kuehlingkuehling/RepRap-Industrial/DXF/frame-enclosure_base-bottom.dxf

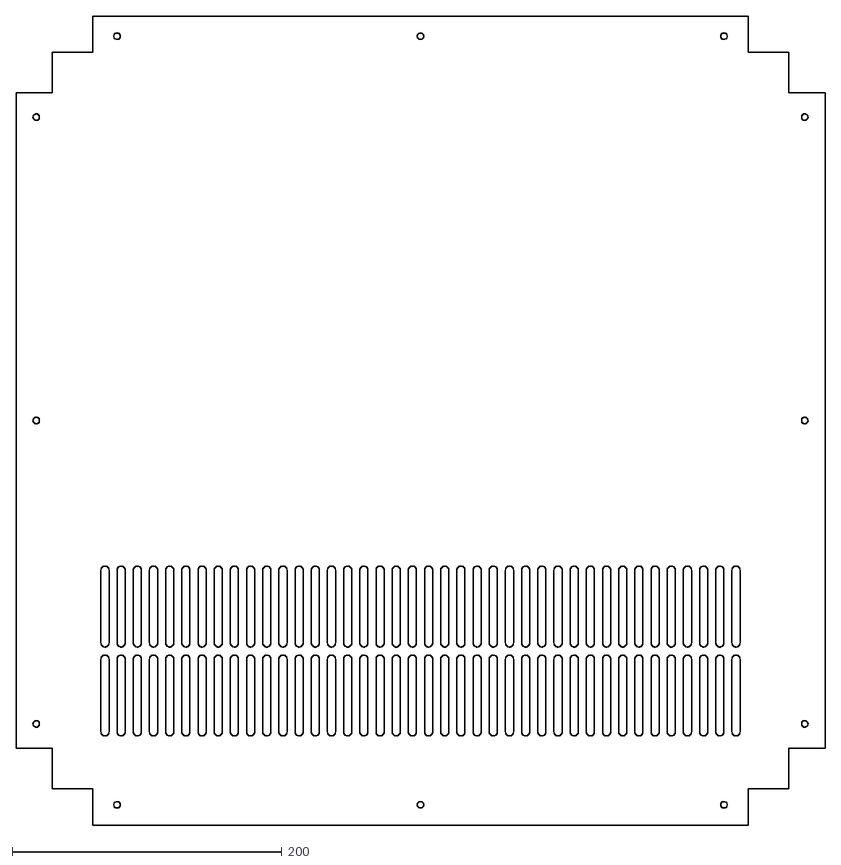
[picture p15: CAD file, 2014-06-27]
DXF/frame-enclosure_base-bottom.dxf
600.0 x 600.0
