kuehlingkuehling/RepRap-Industrial/STL/18___air-filter_activatedcarbon-container-lid.stl

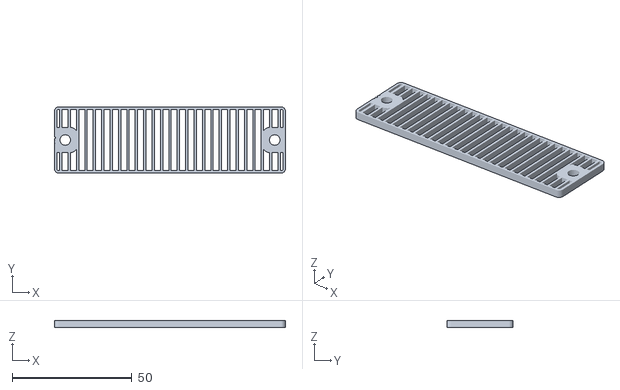
[picture p16: CAD file, 2015-10-23]
STL/18___air-filter_activatedcarbon-container-lid.stl
96.3 x 27.6 x 3.00
