kuehlingkuehling/RepRap-Industrial/DXF/frame-enclosure_chamber-top.dxf

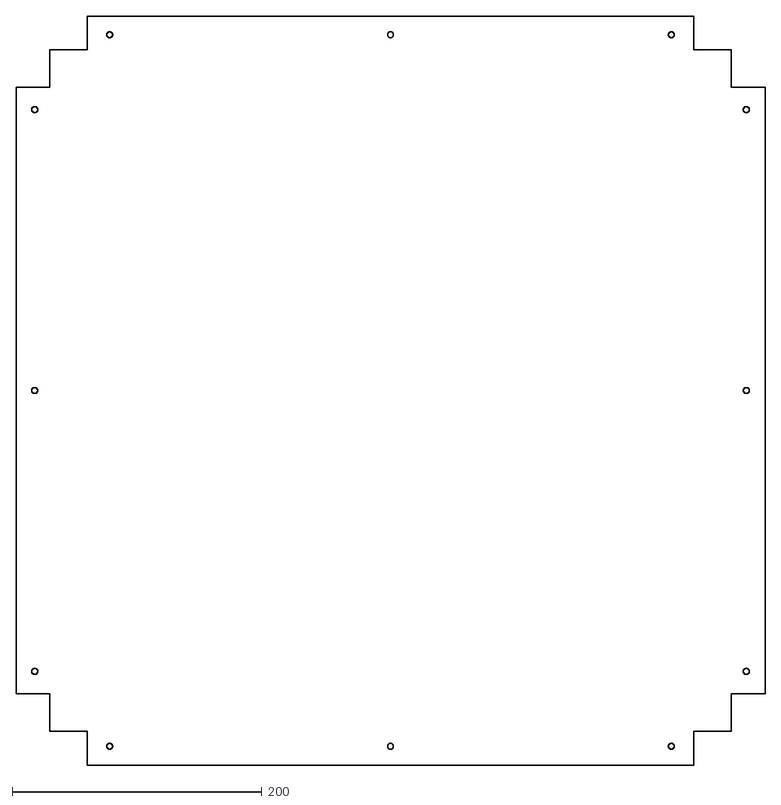
[picture p17: CAD file, 2014-06-27]
DXF/frame-enclosure_chamber-top.dxf
600.0 x 600.0
