kuehlingkuehling/RepRap-Industrial/STL/70___frame-corner_door-top-right.stl

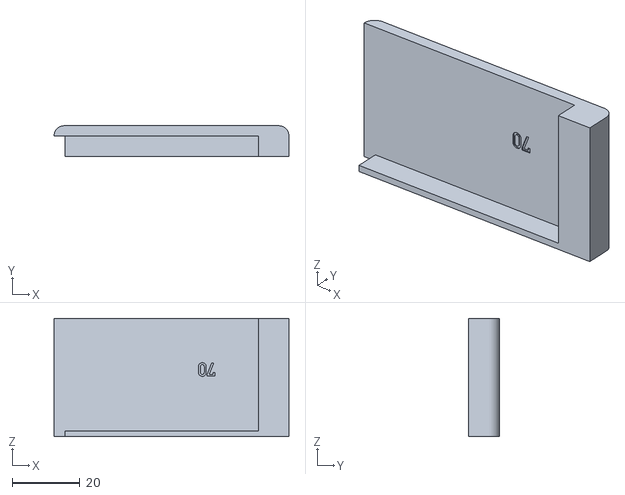
[picture p18: CAD file, 2015-10-23]
STL/70___frame-corner_door-top-right.stl
69.2 x 8.99 x 34.8
