kuehlingkuehling/RepRap-Industrial/DXF/frame-enclosure_base-front.dxf

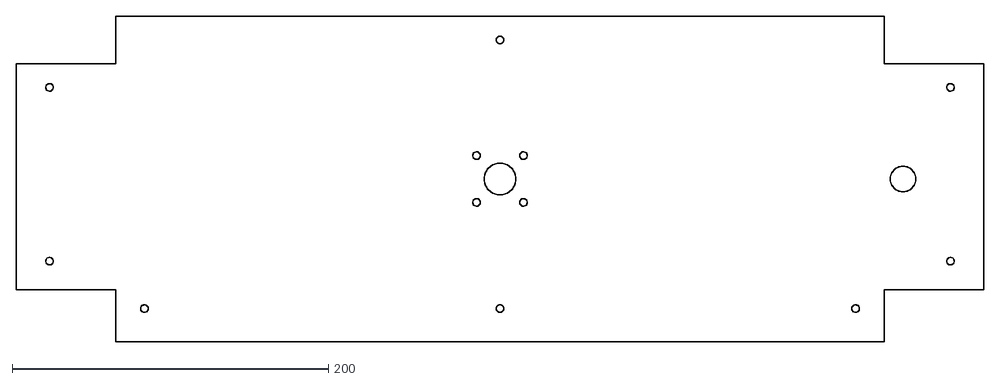
[picture p19: CAD file, 2014-06-27]
DXF/frame-enclosure_base-front.dxf
612.0 x 206.0
