kuehlingkuehling/RepRap-Industrial/STL/23___z-end_top.stl

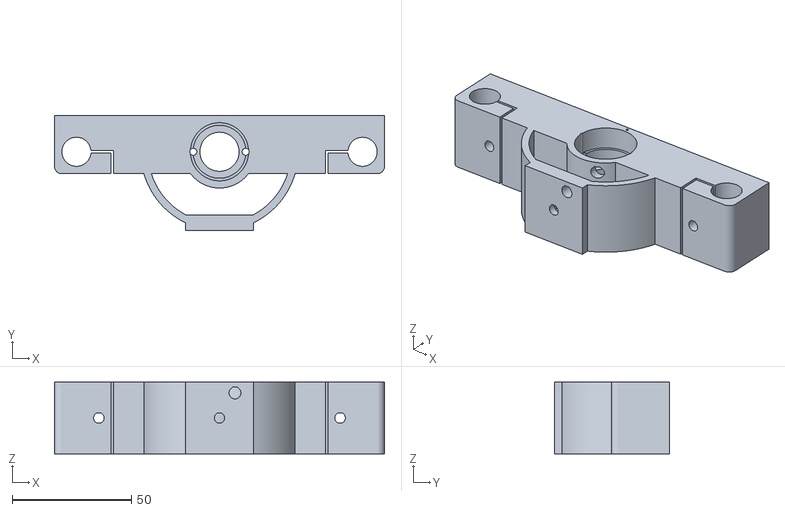
[picture p20: CAD file, 2015-10-23]
STL/23___z-end_top.stl
138.4 x 48.2 x 30.0
