kuehlingkuehling/RepRap-Industrial/STL/290___led-mount_right.stl

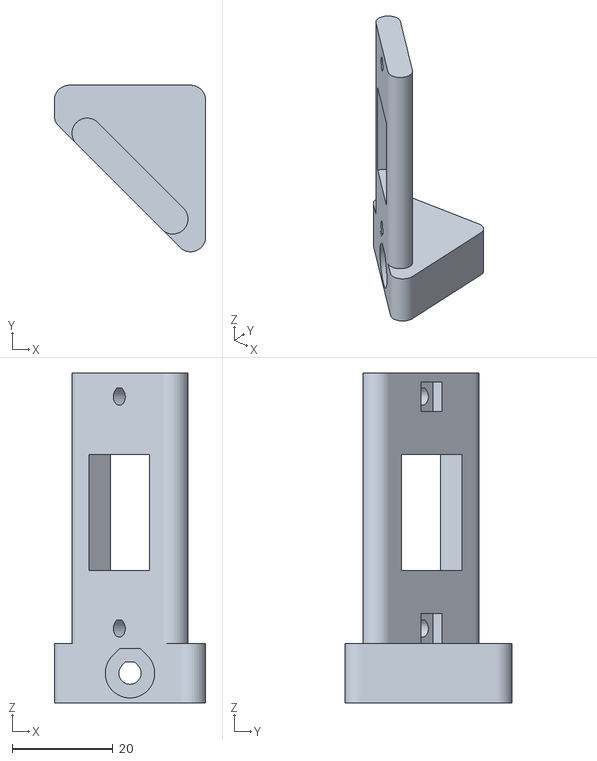
[picture p21: CAD file, 2015-10-23]
STL/290___led-mount_right.stl
30.0 x 33.0 x 65.3
