kuehlingkuehling/RepRap-Industrial/STL/335___bed-corner_front-right_back-left.stl

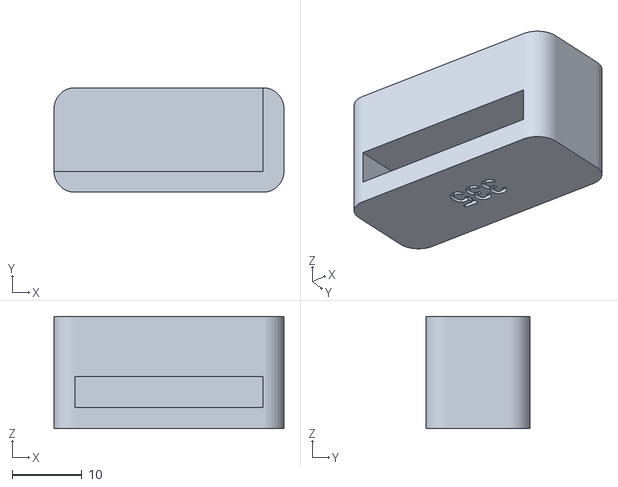
[picture p22: CAD file, 2015-10-23]
STL/335___bed-corner_front-right_back-left.stl
33.0 x 15.0 x 16.1
