kuehlingkuehling/RepRap-Industrial/STL/22___extruder-front.stl

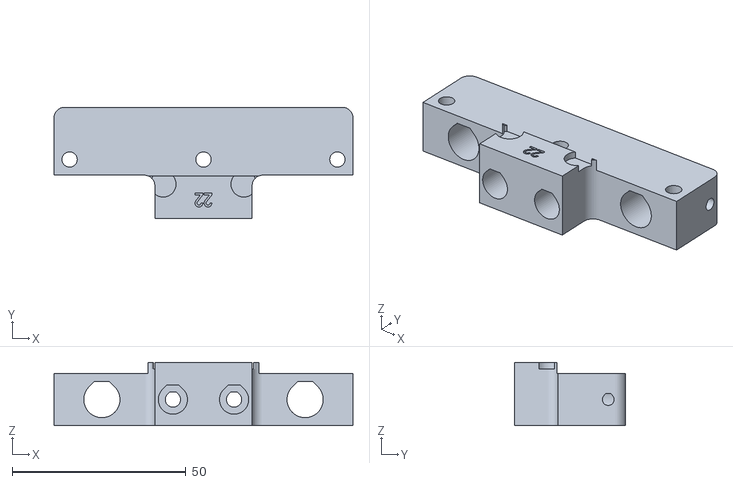
[picture p23: CAD file, 2015-10-23]
STL/22___extruder-front.stl
86.0 x 32.0 x 18.2
