kuehlingkuehling/RepRap-Industrial/STL/264___filament-feed.stl

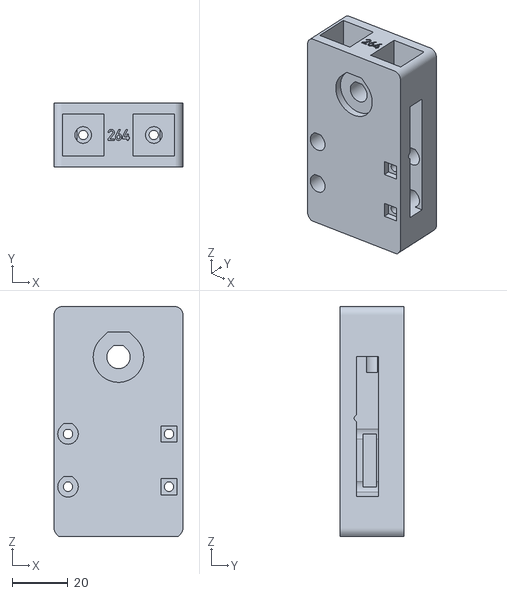
[picture p24: CAD file, 2015-10-23]
STL/264___filament-feed.stl
46.4 x 23.0 x 82.8
