kuehlingkuehling/RepRap-Industrial/STL/29___controller-ethernet-coupling-panel.stl

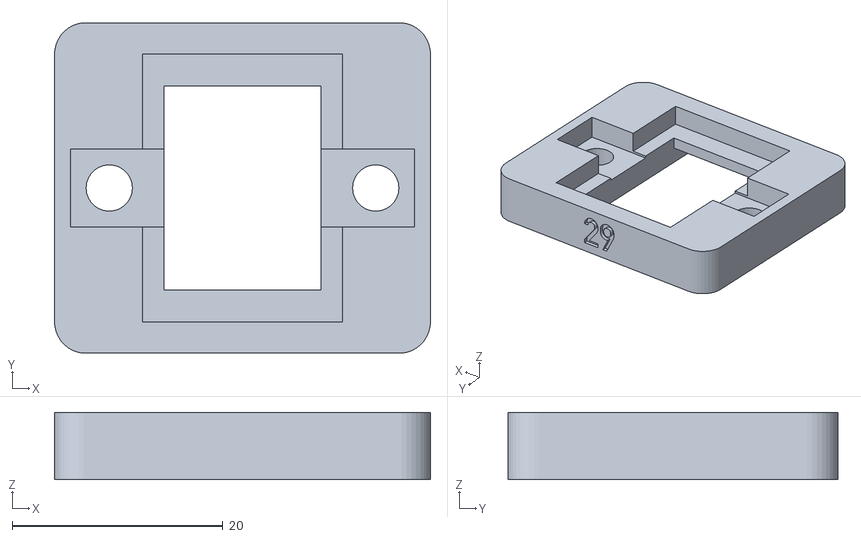
[picture p25: CAD file, 2015-10-23]
STL/29___controller-ethernet-coupling-panel.stl
35.7 x 31.4 x 6.40
