kuehlingkuehling/RepRap-Industrial/STL/53___air-heater-bottom.stl

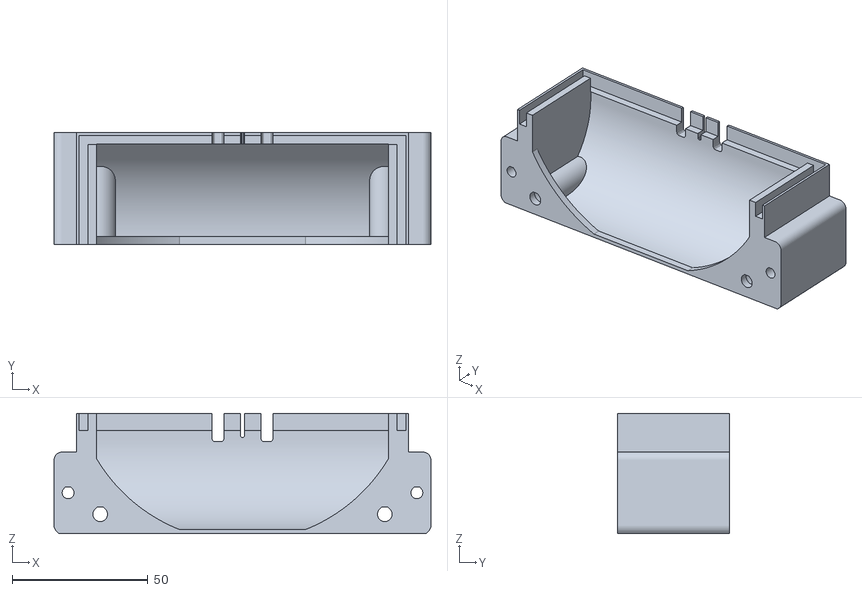
[picture p26: CAD file, 2015-10-23]
STL/53___air-heater-bottom.stl
138.8 x 41.2 x 44.2
