kuehlingkuehling/RepRap-Industrial/STL/31___y-end_back-left.stl

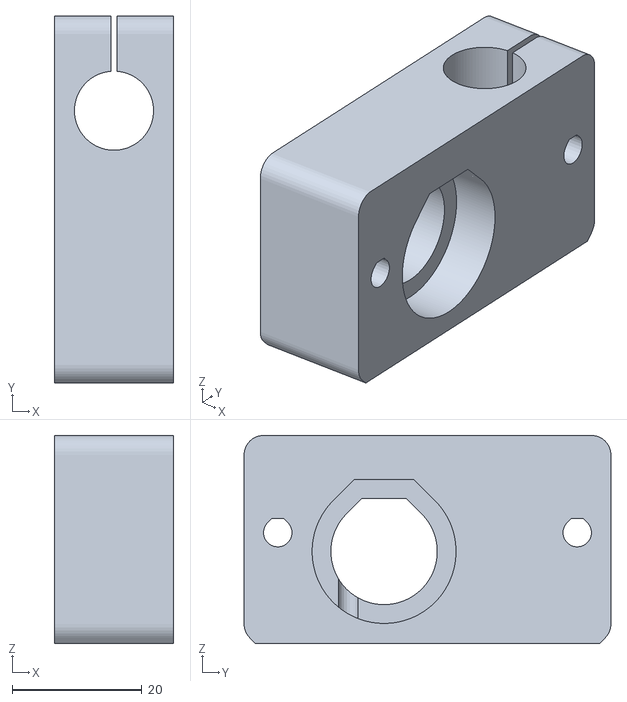
[picture p27: CAD file, 2015-10-23]
STL/31___y-end_back-left.stl
18.4 x 56.6 x 32.1
