kuehlingkuehling/RepRap-Industrial/STL/65___pulley_x-idler_y-idler.stl

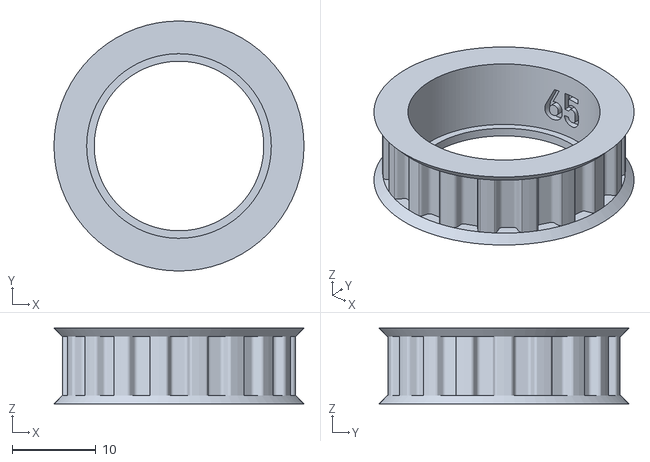
[picture p28: CAD file, 2015-10-23]
STL/65___pulley_x-idler_y-idler.stl
29.8 x 29.8 x 9.00
