kuehlingkuehling/RepRap-Industrial/STL/56___cablechain-mount-y-frame_back.stl

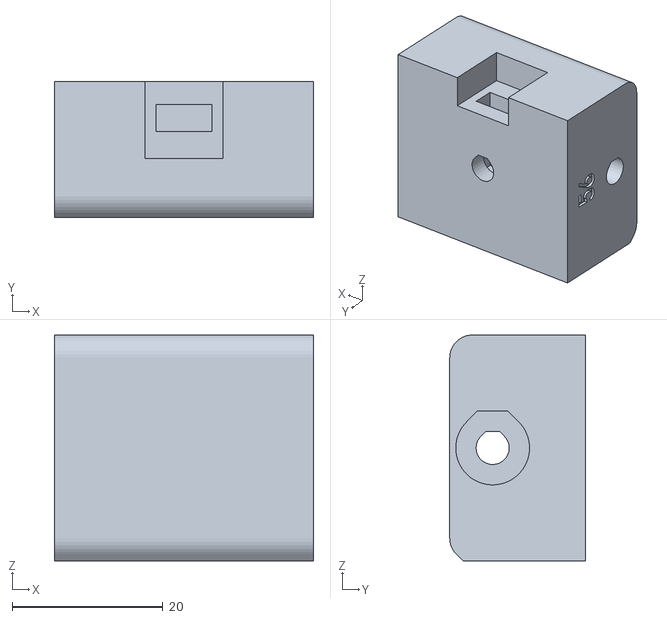
[picture p29: CAD file, 2015-10-23]
STL/56___cablechain-mount-y-frame_back.stl
34.4 x 18.0 x 30.0
