kuehlingkuehling/RepRap-Industrial/STL/17___belt-tensioner_y-right_x.stl

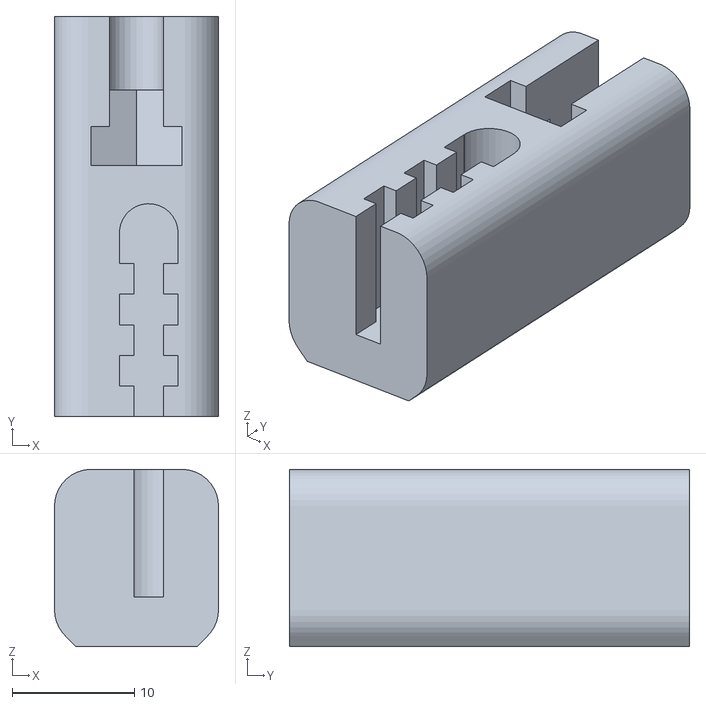
[picture p30: CAD file, 2015-10-23]
STL/17___belt-tensioner_y-right_x.stl
13.4 x 32.7 x 14.5
