kuehlingkuehling/RepRap-Industrial/STL/20___air-filter_activatedcarbon-container.stl

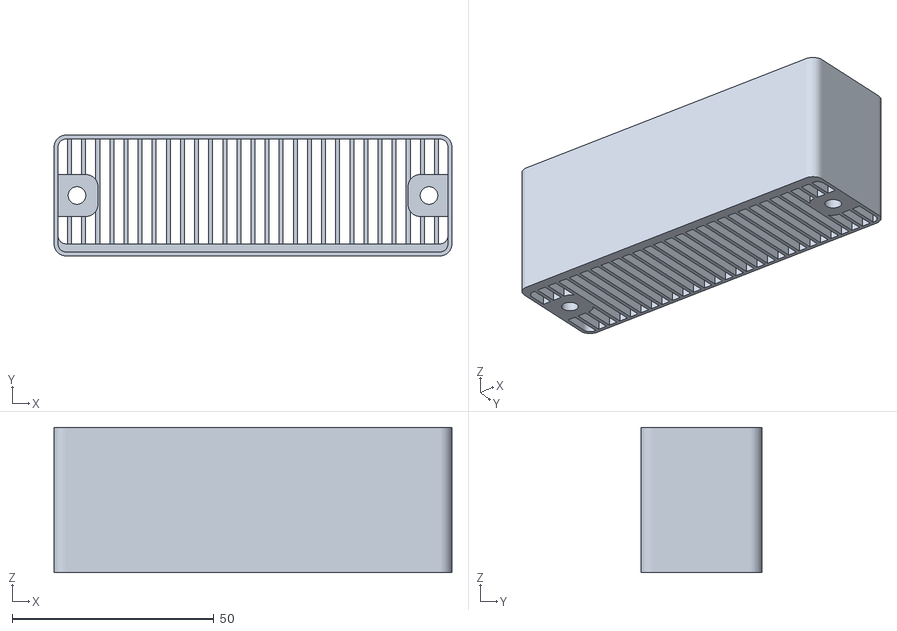
[picture p31: CAD file, 2015-10-23]
STL/20___air-filter_activatedcarbon-container.stl
98.7 x 30.0 x 36.0
