kuehlingkuehling/RepRap-Industrial/STL/13___frame-enclosure-door-handle.stl

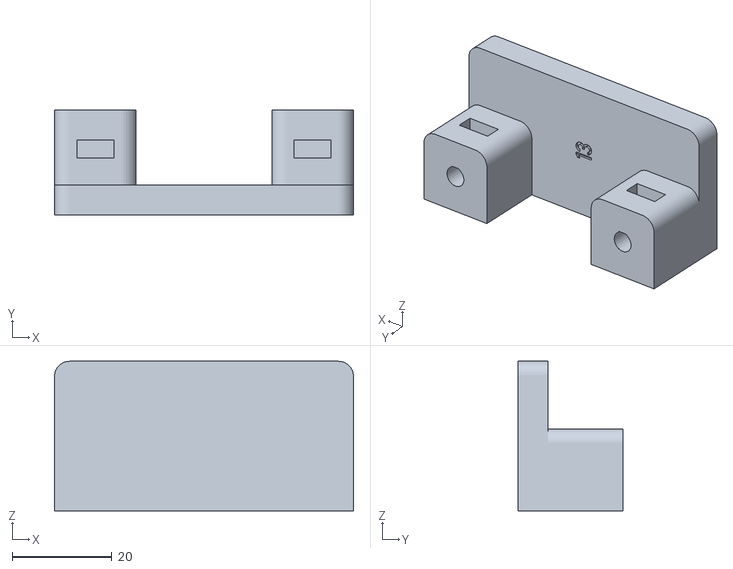
[picture p32: CAD file, 2015-10-23]
STL/13___frame-enclosure-door-handle.stl
60.0 x 21.0 x 30.0
