kuehlingkuehling/RepRap-Industrial/STL/275___frame-enclosure-cable-feedthrough_10.stl

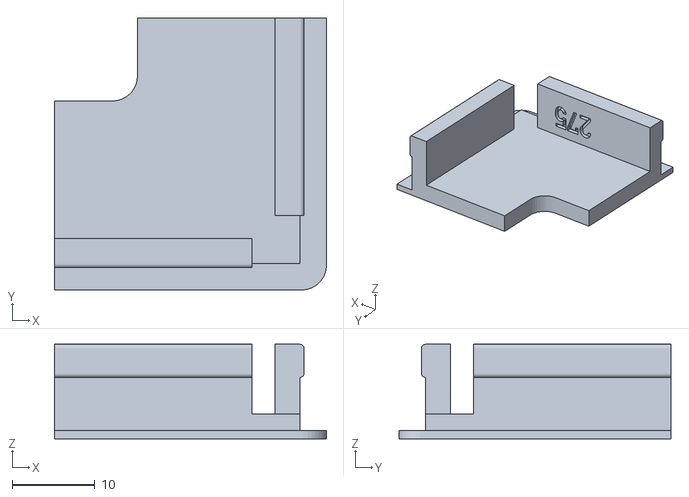
[picture p33: CAD file, 2015-10-23]
STL/275___frame-enclosure-cable-feedthrough_10.stl
32.8 x 32.8 x 11.4
