kuehlingkuehling/RepRap-Industrial/STL/35___frame-corner_top-back_bottom.stl

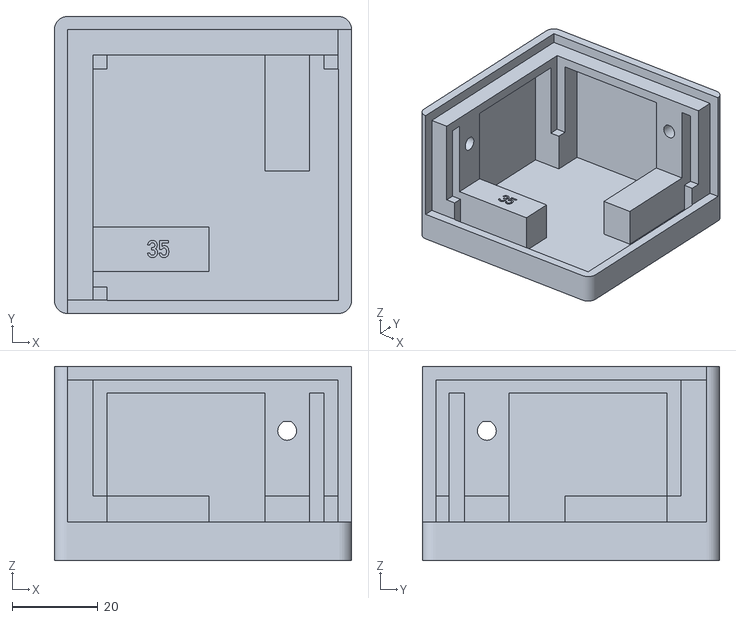
[picture p34: CAD file, 2015-10-23]
STL/35___frame-corner_top-back_bottom.stl
69.2 x 69.2 x 45.2
