kuehlingkuehling/RepRap-Industrial/STL/27___spool-mount-endcap.stl

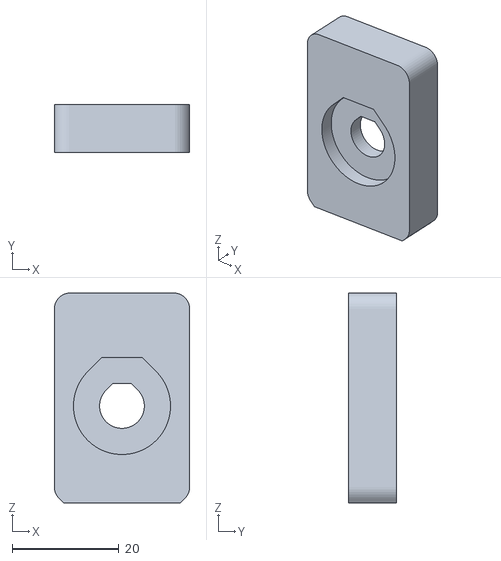
[picture p35: CAD file, 2015-10-23]
STL/27___spool-mount-endcap.stl
25.4 x 9.00 x 39.4
