kuehlingkuehling/RepRap-Industrial/STL/66___air-heater-top.stl

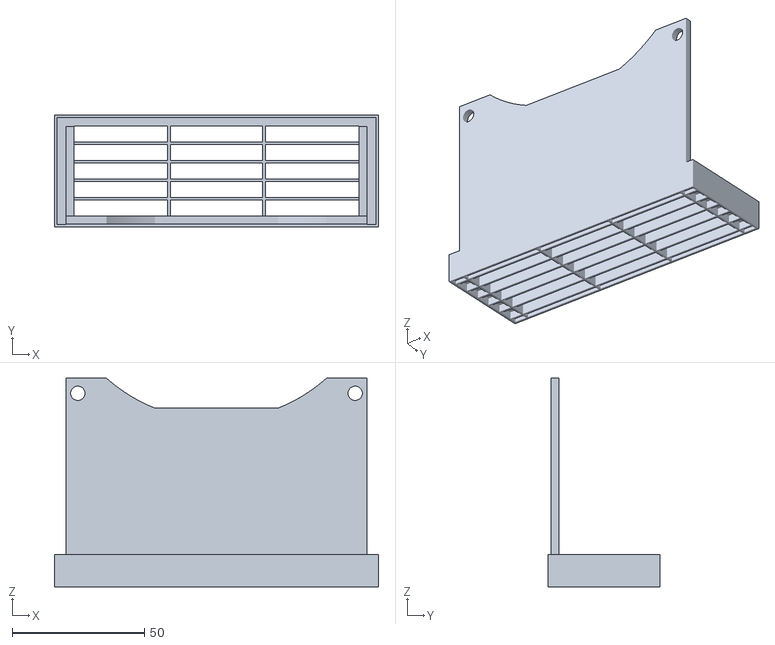
[picture p36: CAD file, 2015-10-23]
STL/66___air-heater-top.stl
122.4 x 42.4 x 78.8
