kuehlingkuehling/RepRap-Industrial/STL/57___y-end_front-right.stl

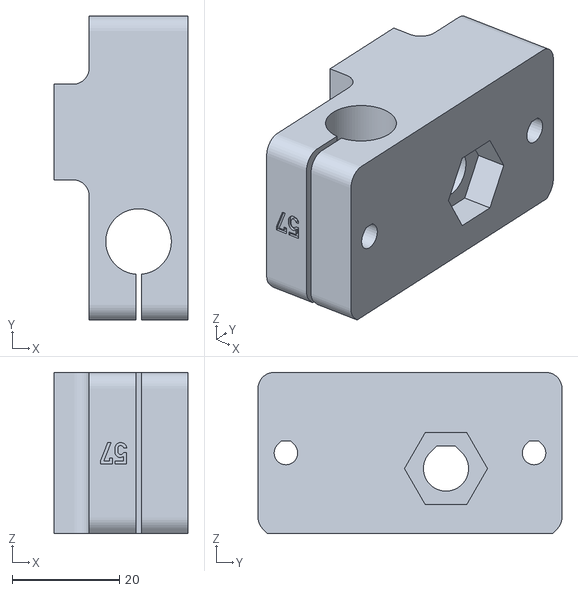
[picture p37: CAD file, 2015-10-23]
STL/57___y-end_front-right.stl
24.9 x 56.6 x 30.0
