kuehlingkuehling/RepRap-Industrial/STL/16___frame-corner_door-bottom-right.stl

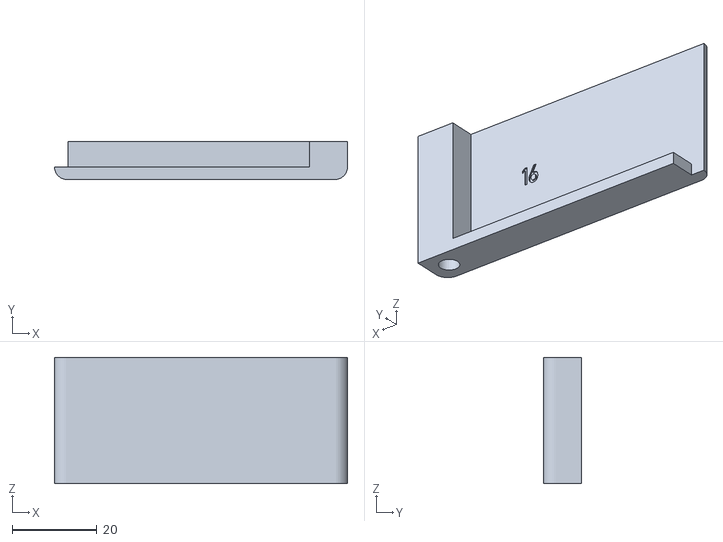
[picture p38: CAD file, 2015-10-23]
STL/16___frame-corner_door-bottom-right.stl
69.2 x 8.99 x 29.8
