kuehlingkuehling/RepRap-Industrial/STL/277___frame-enclosure-cable-feedthrough_20.stl

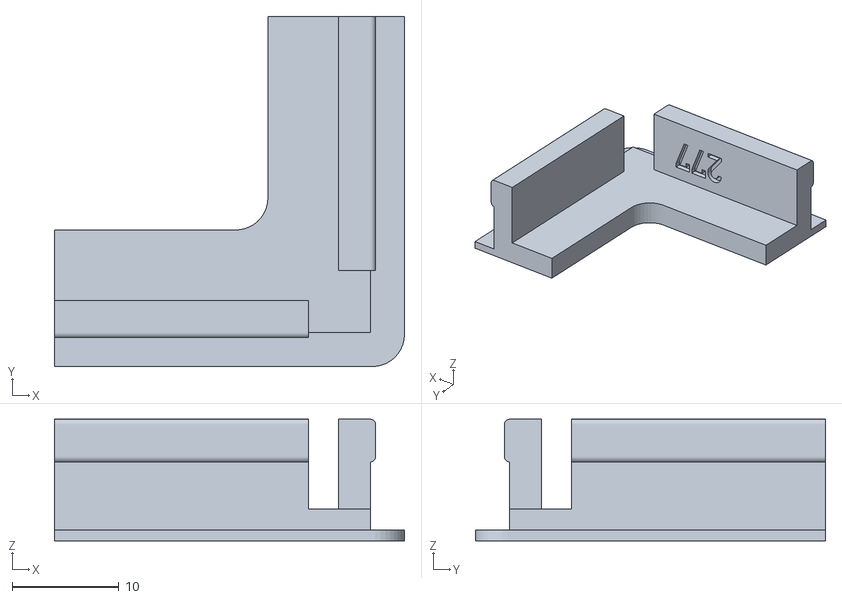
[picture p39: CAD file, 2015-10-23]
STL/277___frame-enclosure-cable-feedthrough_20.stl
32.8 x 32.8 x 11.4
