kuehlingkuehling/RepRap-Industrial/STL/40___frame-corner_top-front-left.stl

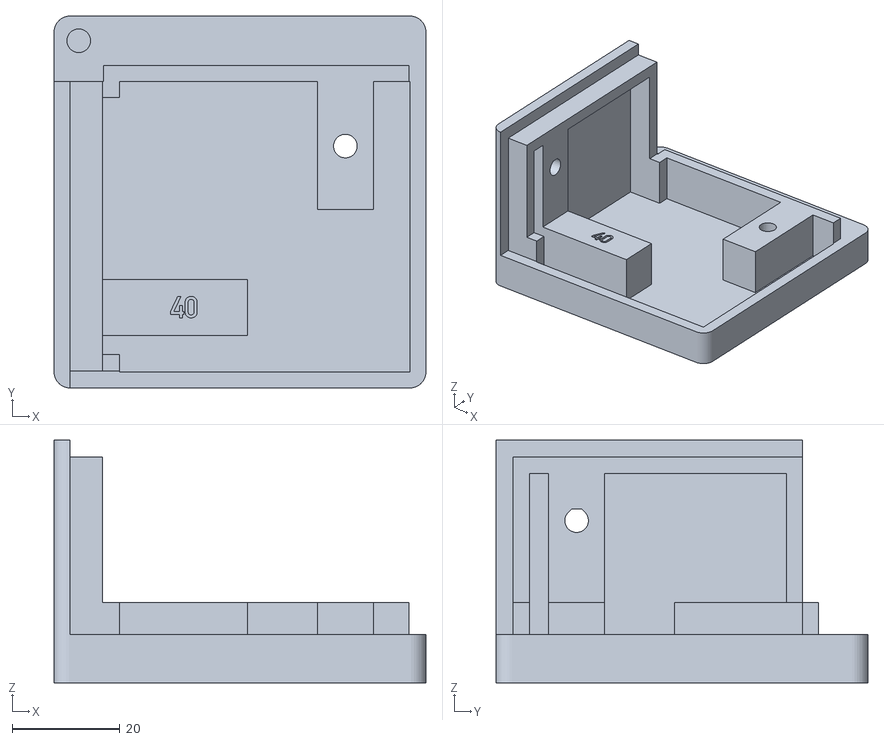
[picture p40: CAD file, 2015-10-23]
STL/40___frame-corner_top-front-left.stl
69.2 x 69.2 x 45.2
