kuehlingkuehling/RepRap-Industrial/STL/33___z-motor-mount.stl

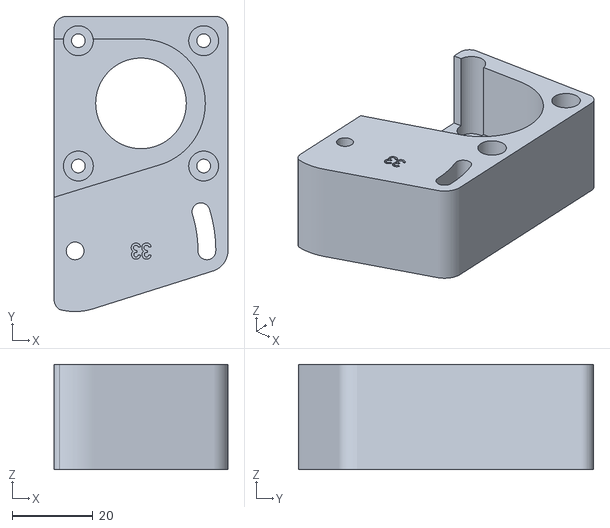
[picture p41: CAD file, 2015-10-23]
STL/33___z-motor-mount.stl
43.0 x 73.0 x 26.0
