kuehlingkuehling/RepRap-Industrial/STL/26___z-bed-mount.stl

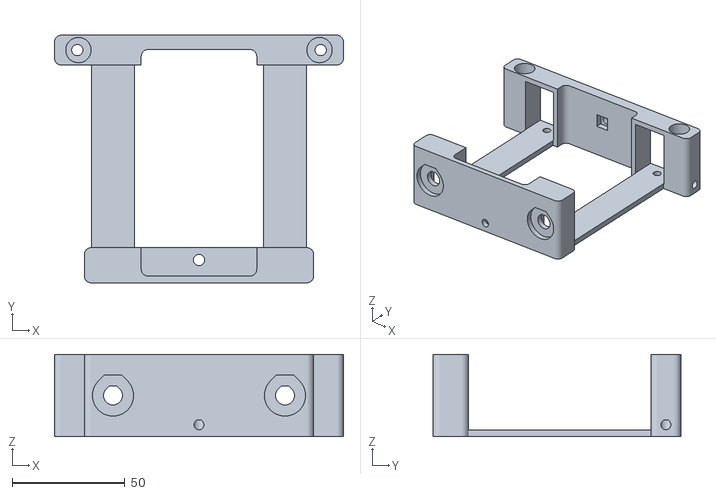
[picture p42: CAD file, 2015-10-23]
STL/26___z-bed-mount.stl
128.0 x 109.7 x 36.4
