kuehlingkuehling/RepRap-Industrial/STL/34___frame-corner_middle-back.stl

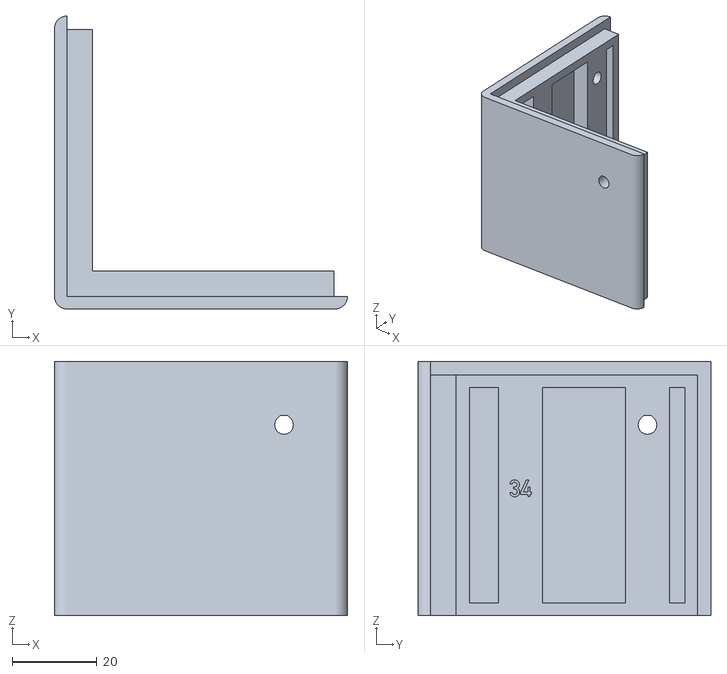
[picture p43: CAD file, 2015-10-23]
STL/34___frame-corner_middle-back.stl
69.2 x 69.2 x 60.0
