kuehlingkuehling/RepRap-Industrial/STL/46___frame-enclosure-angle.stl

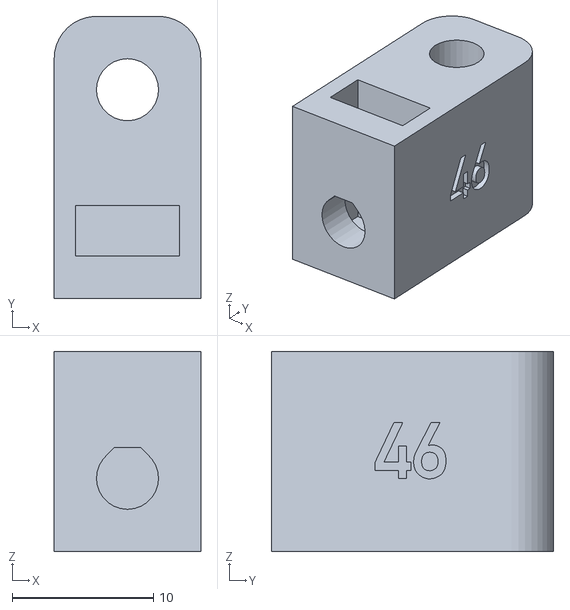
[picture p44: CAD file, 2015-10-23]
STL/46___frame-enclosure-angle.stl
10.4 x 20.0 x 14.2
