kuehlingkuehling/RepRap-Industrial/STL/24___z-end_bottom.stl

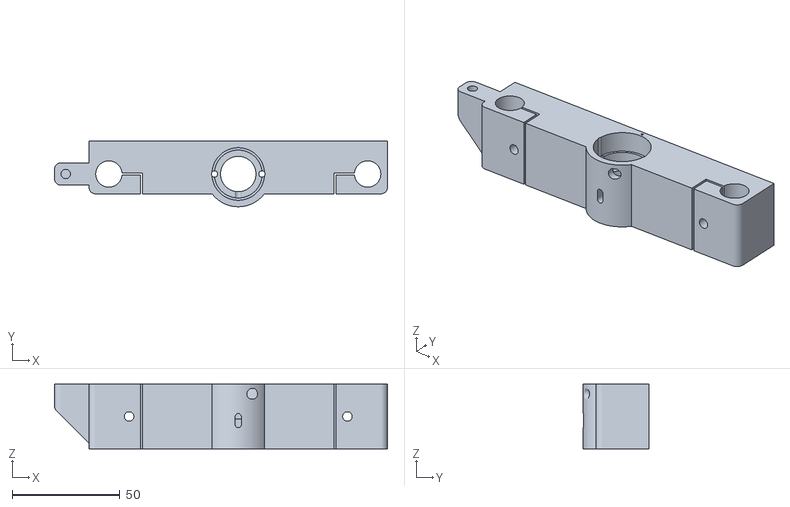
[picture p45: CAD file, 2015-10-23]
STL/24___z-end_bottom.stl
154.4 x 30.4 x 30.0
