kuehlingkuehling/RepRap-Industrial/STL/268___y-endstop-magnet-mount.stl

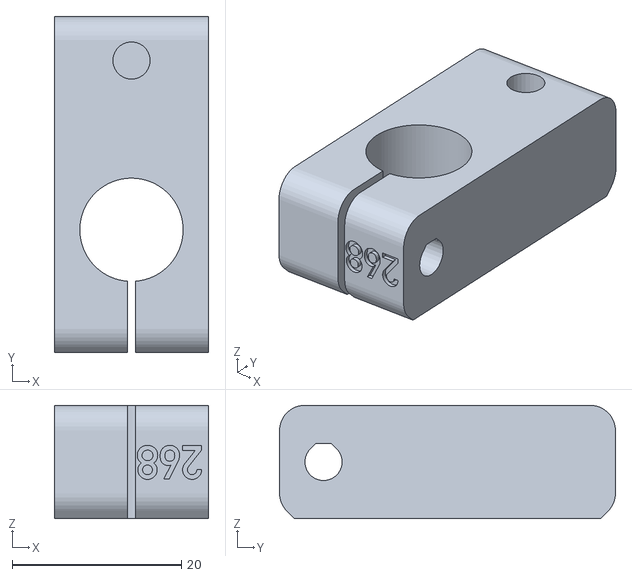
[picture p46: CAD file, 2015-10-23]
STL/268___y-endstop-magnet-mount.stl
18.2 x 39.7 x 13.4
