kuehlingkuehling/RepRap-Industrial/STL/3___extruder-idler_right-front.stl

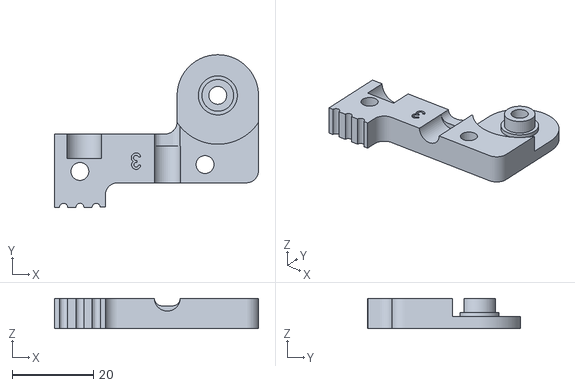
[picture p47: CAD file, 2015-10-23]
STL/3___extruder-idler_right-front.stl
50.1 x 37.5 x 7.40
