kuehlingkuehling/RepRap-Industrial/STL/51___x-end_idler.stl

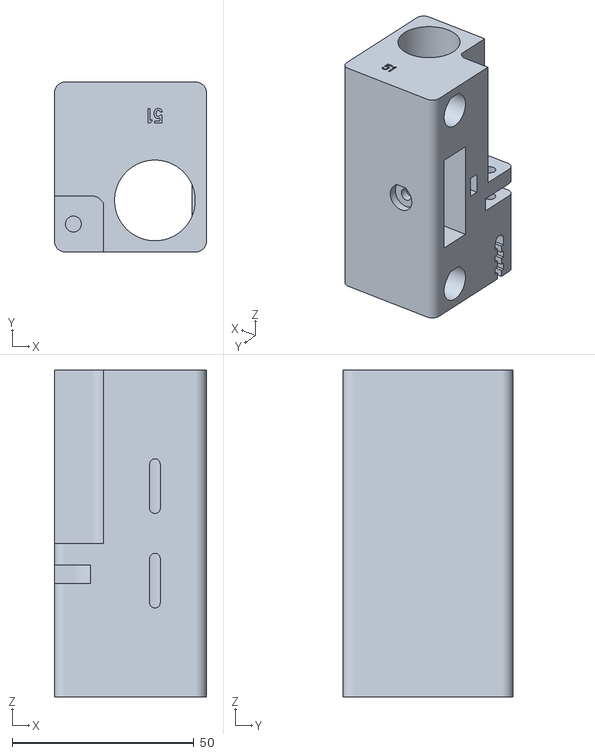
[picture p48: CAD file, 2015-10-23]
STL/51___x-end_idler.stl
41.8 x 46.8 x 90.0
