kuehlingkuehling/RepRap-Industrial/STL/59___x-end_idler-shaft.stl

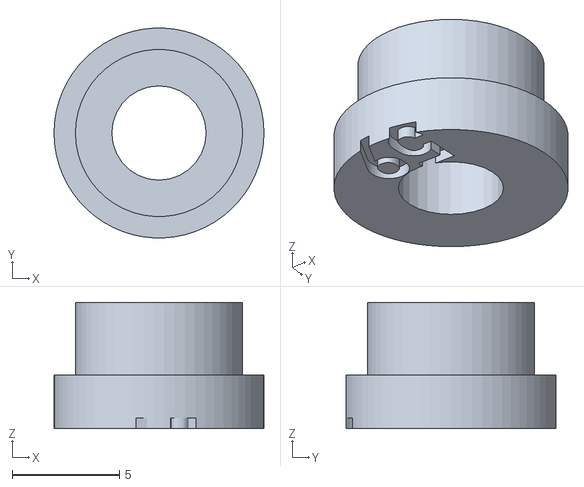
[picture p49: CAD file, 2015-10-23]
STL/59___x-end_idler-shaft.stl
9.80 x 9.79 x 5.90
