kuehlingkuehling/RepRap-Industrial/STL/308___y-arbor-support_bottom.stl

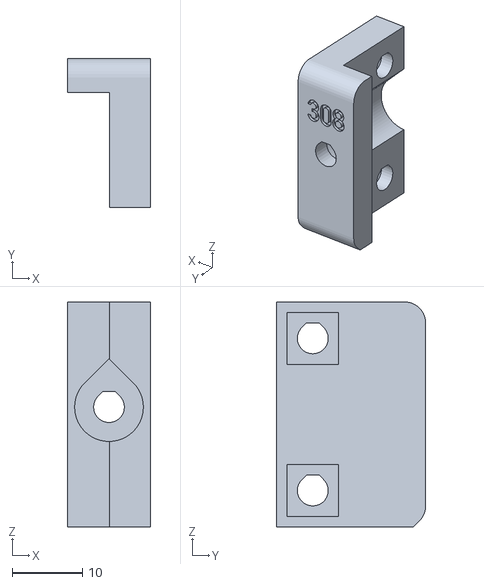
[picture p50: CAD file, 2015-10-23]
STL/308___y-arbor-support_bottom.stl
11.8 x 21.3 x 32.1
