kuehlingkuehling/RepRap-Industrial/STL/2___y-motor-mount.stl

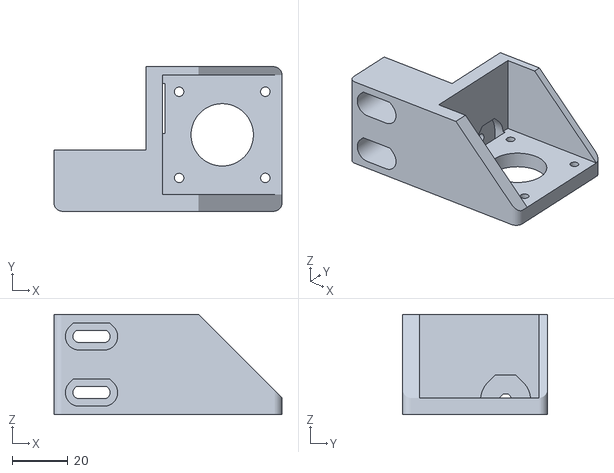
[picture p51: CAD file, 2015-10-23]
STL/2___y-motor-mount.stl
82.0 x 52.0 x 36.0
