kuehlingkuehling/RepRap-Industrial/STL/72___x-carriage.stl

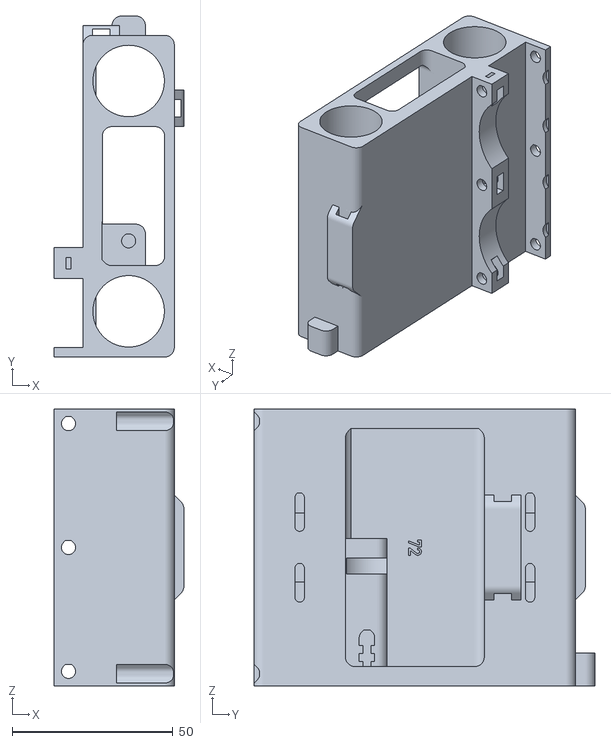
[picture p52: CAD file, 2015-10-23]
STL/72___x-carriage.stl
40.4 x 106.0 x 86.0
