kuehlingkuehling/RepRap-Industrial/STL/44___pcb-mount_rumba-right.stl

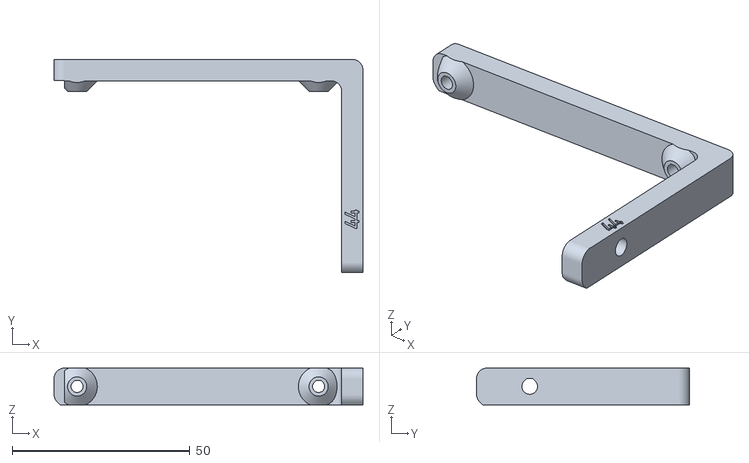
[picture p53: CAD file, 2015-10-23]
STL/44___pcb-mount_rumba-right.stl
87.0 x 60.0 x 10.4
