kuehlingkuehling/RepRap-Industrial/STL/38___extruder-back.stl

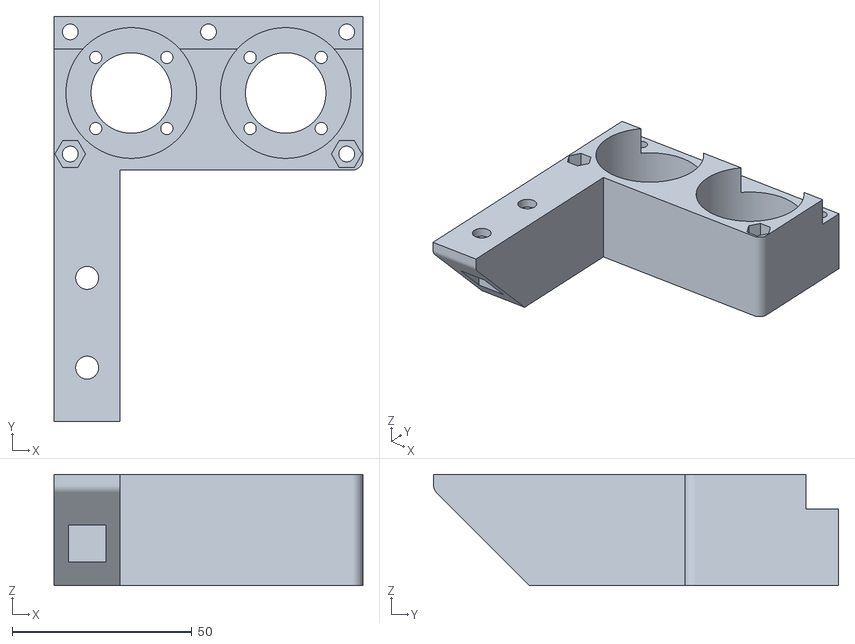
[picture p54: CAD file, 2015-10-23]
STL/38___extruder-back.stl
86.0 x 112.8 x 31.0
