kuehlingkuehling/RepRap-Industrial/STL/307___y-arbor-support_top.stl

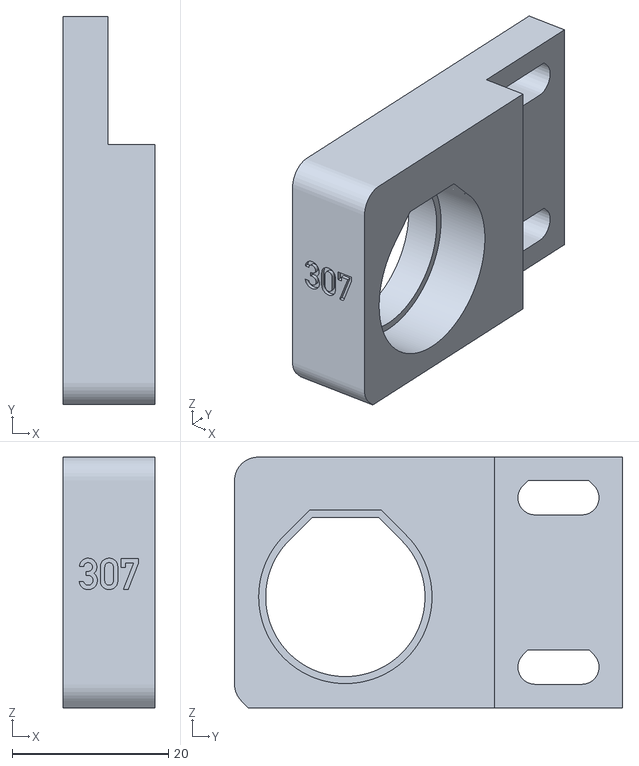
[picture p55: CAD file, 2015-10-23]
STL/307___y-arbor-support_top.stl
11.8 x 49.7 x 32.1
