kuehlingkuehling/RepRap-Industrial/STL/41___air-filter_fan-duct.stl

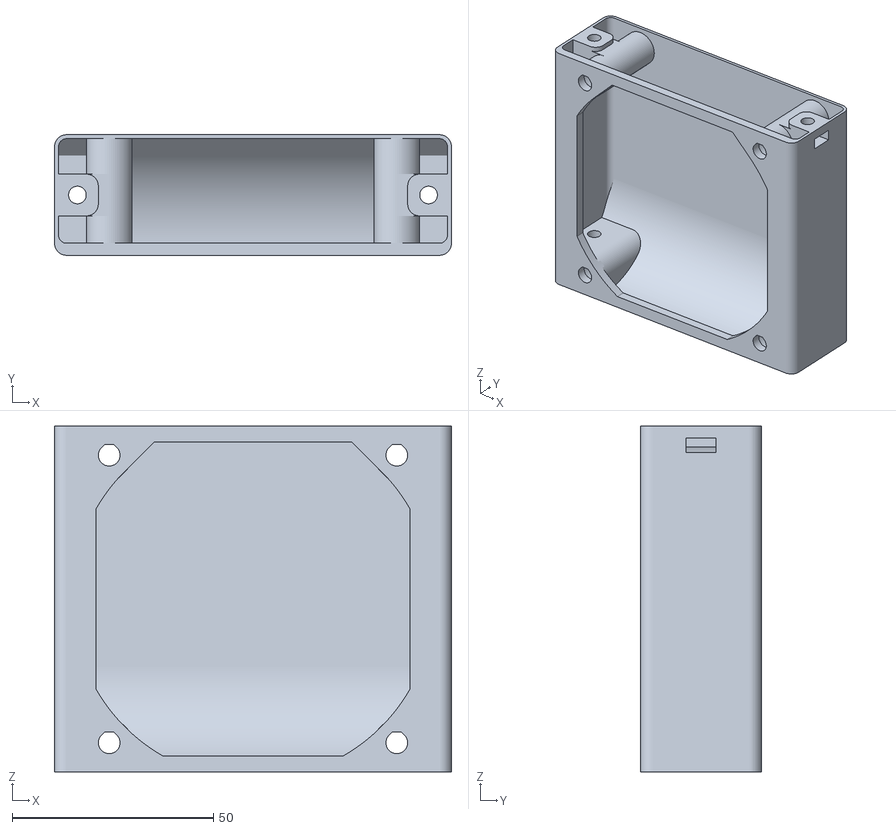
[picture p56: CAD file, 2015-10-23]
STL/41___air-filter_fan-duct.stl
98.7 x 30.0 x 86.0
