kuehlingkuehling/RepRap-Industrial/STL/351___bed-leveling-mount.stl

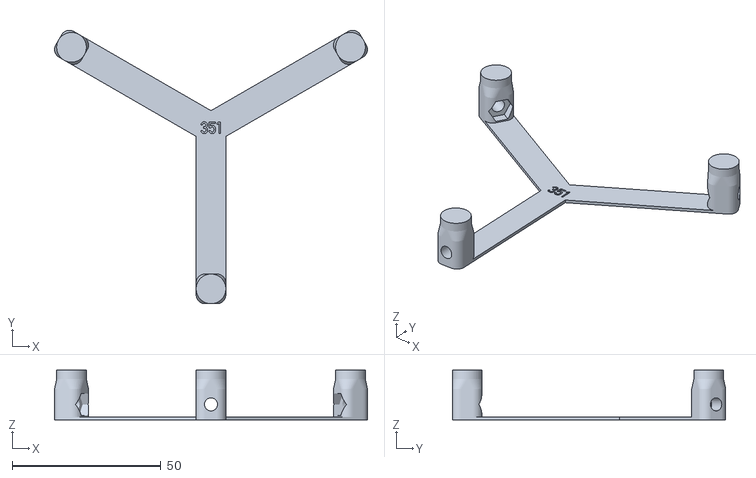
[picture p57: CAD file, 2015-10-23]
STL/351___bed-leveling-mount.stl
105.3 x 92.0 x 16.7
