kuehlingkuehling/RepRap-Industrial/STL/42___cablechain-mount-y-frame_front.stl

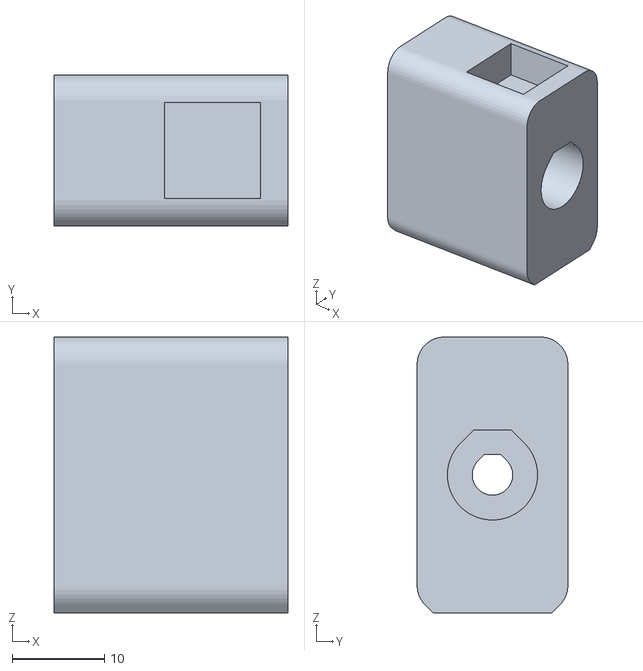
[picture p58: CAD file, 2015-10-23]
STL/42___cablechain-mount-y-frame_front.stl
25.4 x 16.4 x 30.0
