kuehlingkuehling/RepRap-Industrial/STL/14___frame-small-mount.stl

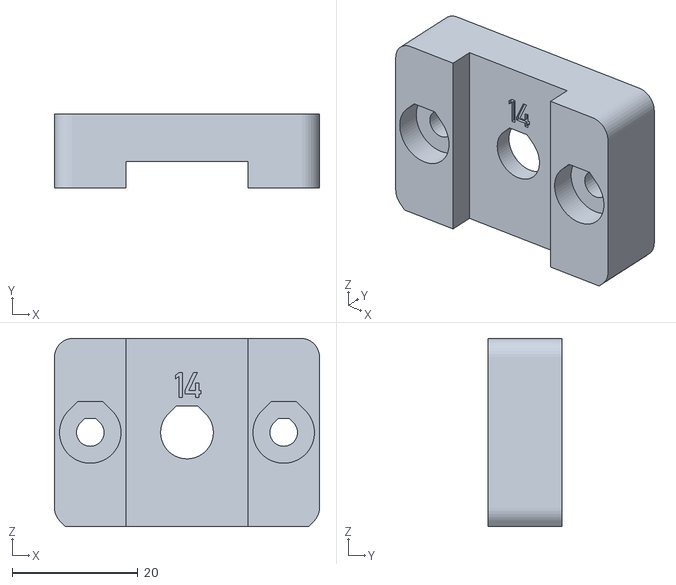
[picture p59: CAD file, 2015-10-23]
STL/14___frame-small-mount.stl
42.2 x 11.8 x 30.0
