kuehlingkuehling/RepRap-Industrial/STL/extruder-flexible-filament-adapter_left.stl

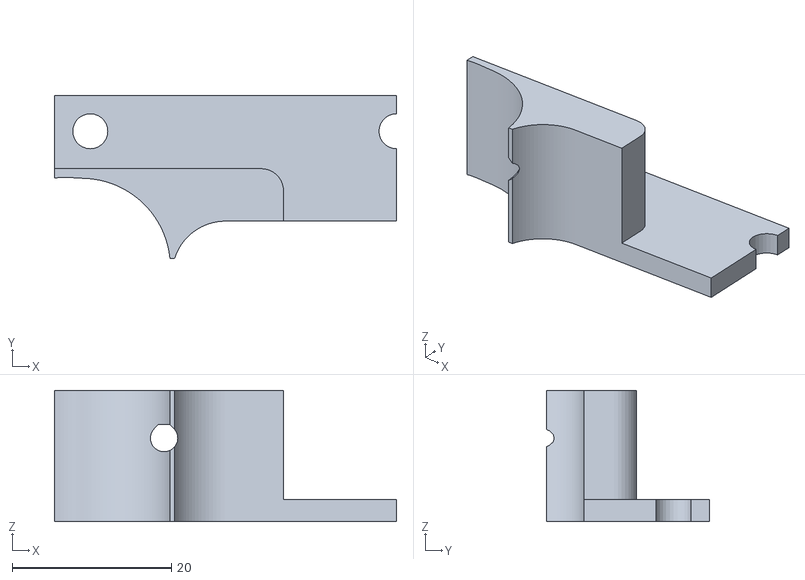
[picture p60: CAD file, 2015-02-20]
STL/extruder-flexible-filament-adapter_left.stl
43.0 x 20.5 x 16.5
